alvarop/usb_c_power/tables/icoarse_table.png

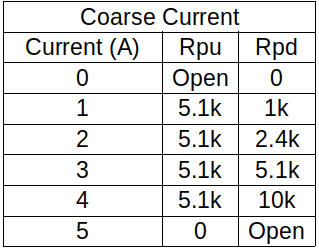
tables/icoarse_table.png
